harshil21/PinPointer/src/rust/rtk/src/lib.rs

pub mod dispatcher;
mod methods;
pub mod parsing;
pub mod port;
pub mod protocol;
pub mod rtcm_parser;

pub use protocol::nmea::{GgaData, GpsFixQuality, GsvConstellation, GsvData};
pub use protocol::response::WireMessage;
